xfacta/Automotive-InputOutput-Circuits/Datsun Gauges Complete.kicad_sch

## KiCad design Datsun Gauges Complete.kicad_sch (2024-01-28)

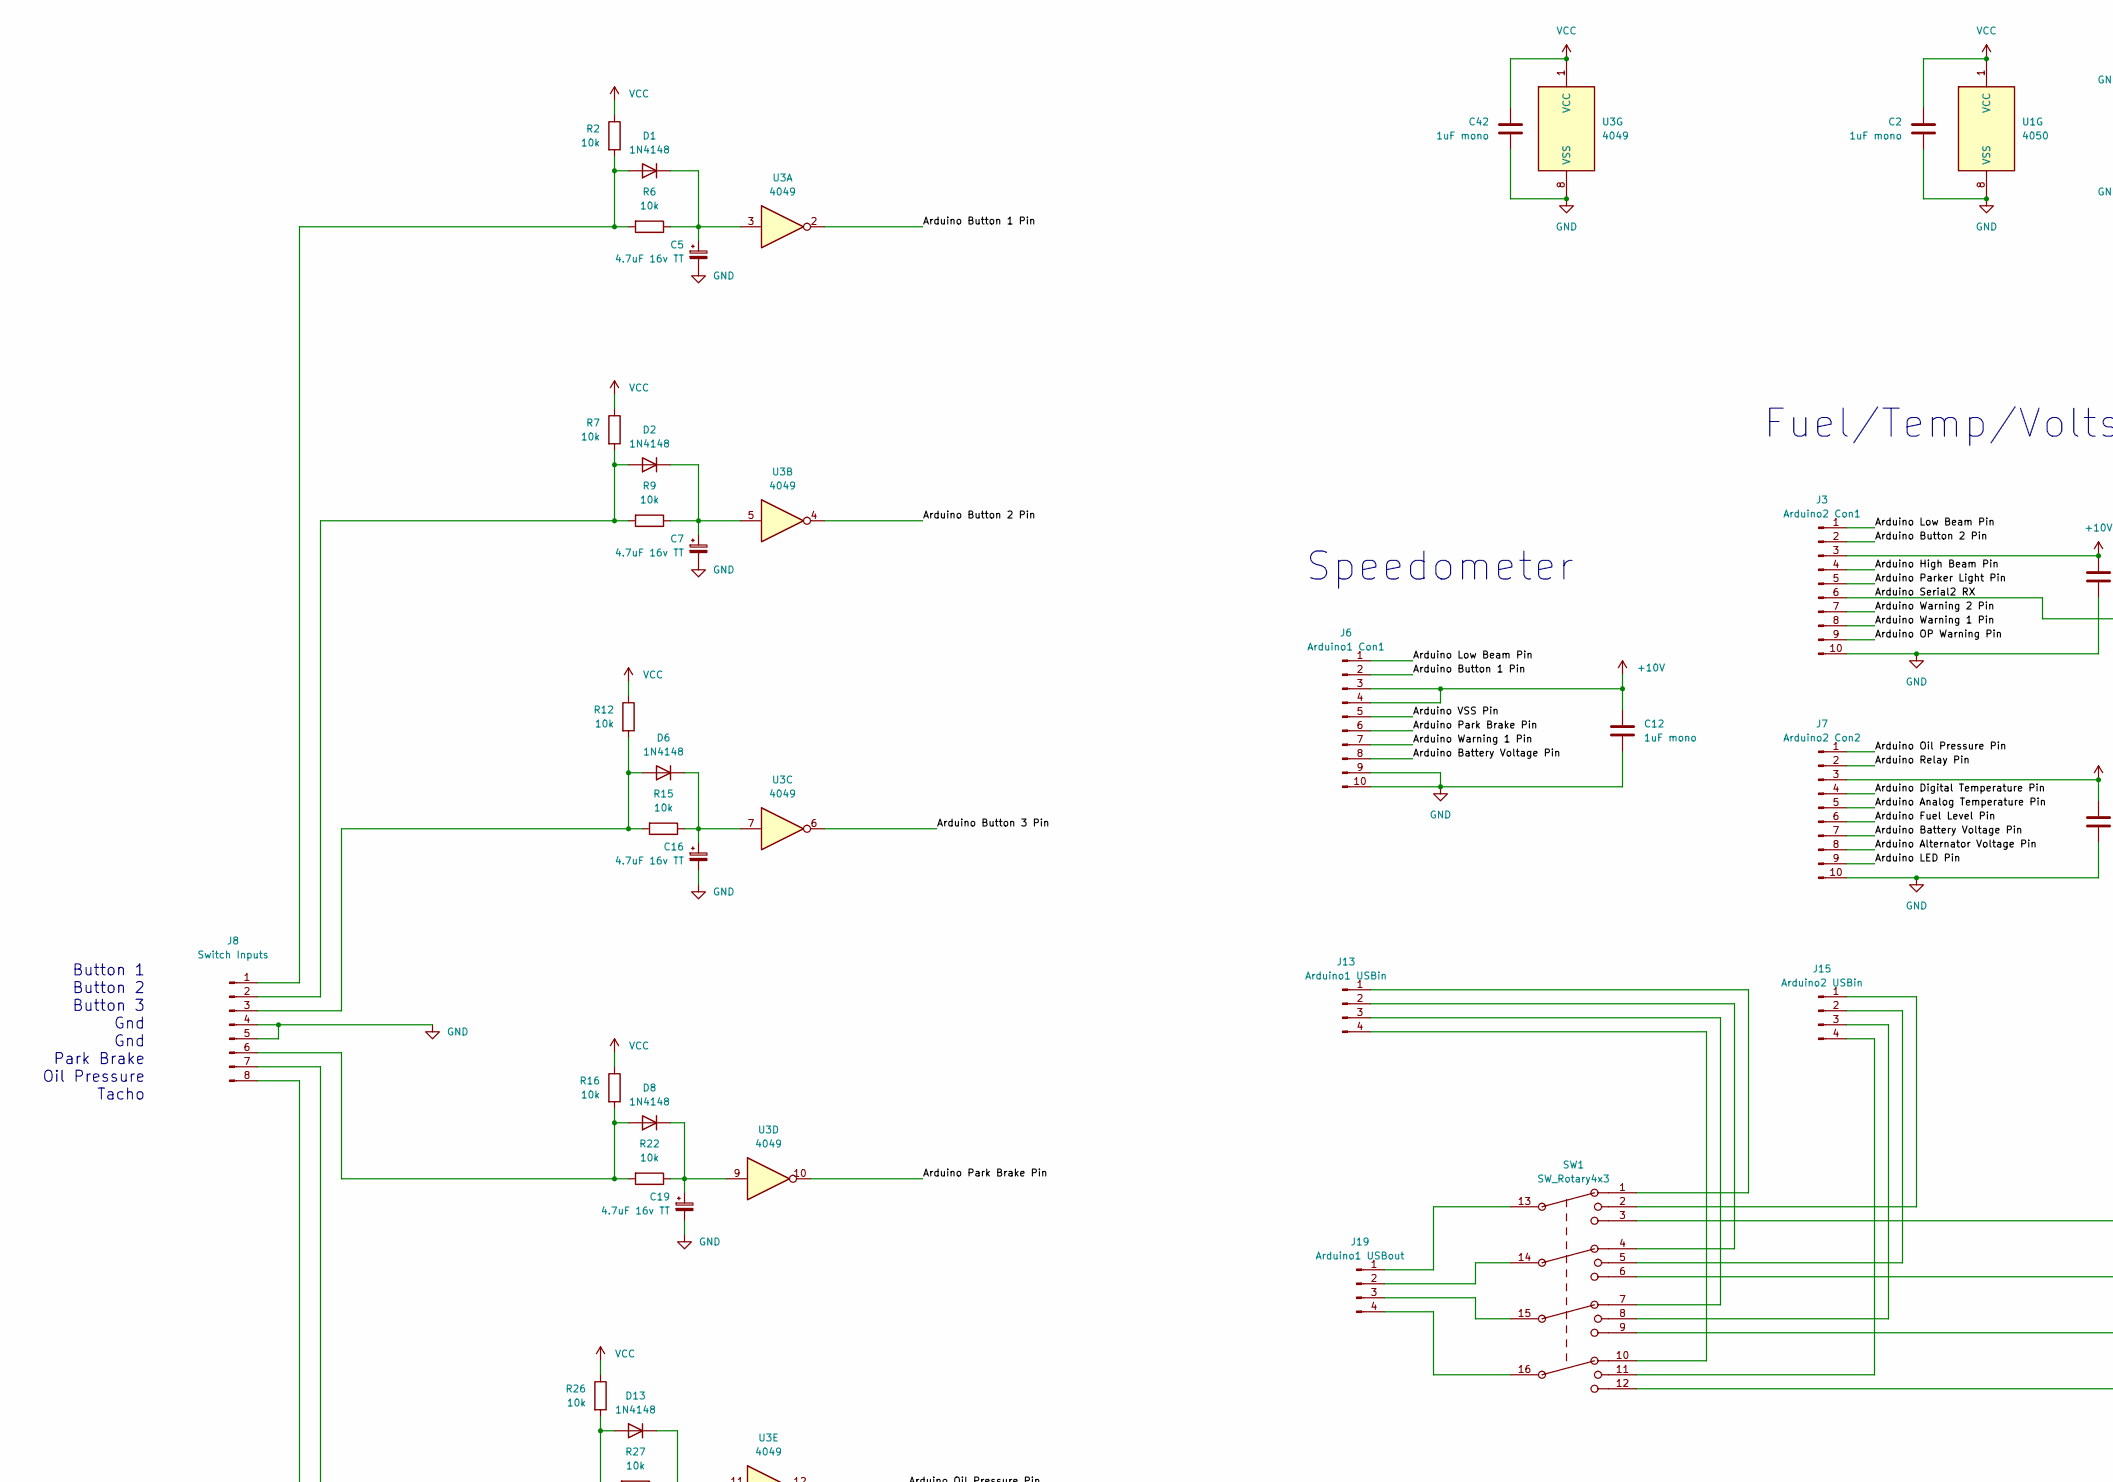
[picture p4: schematic Datsun Gauges Complete.kicad_sch, part in row 1, column 1]

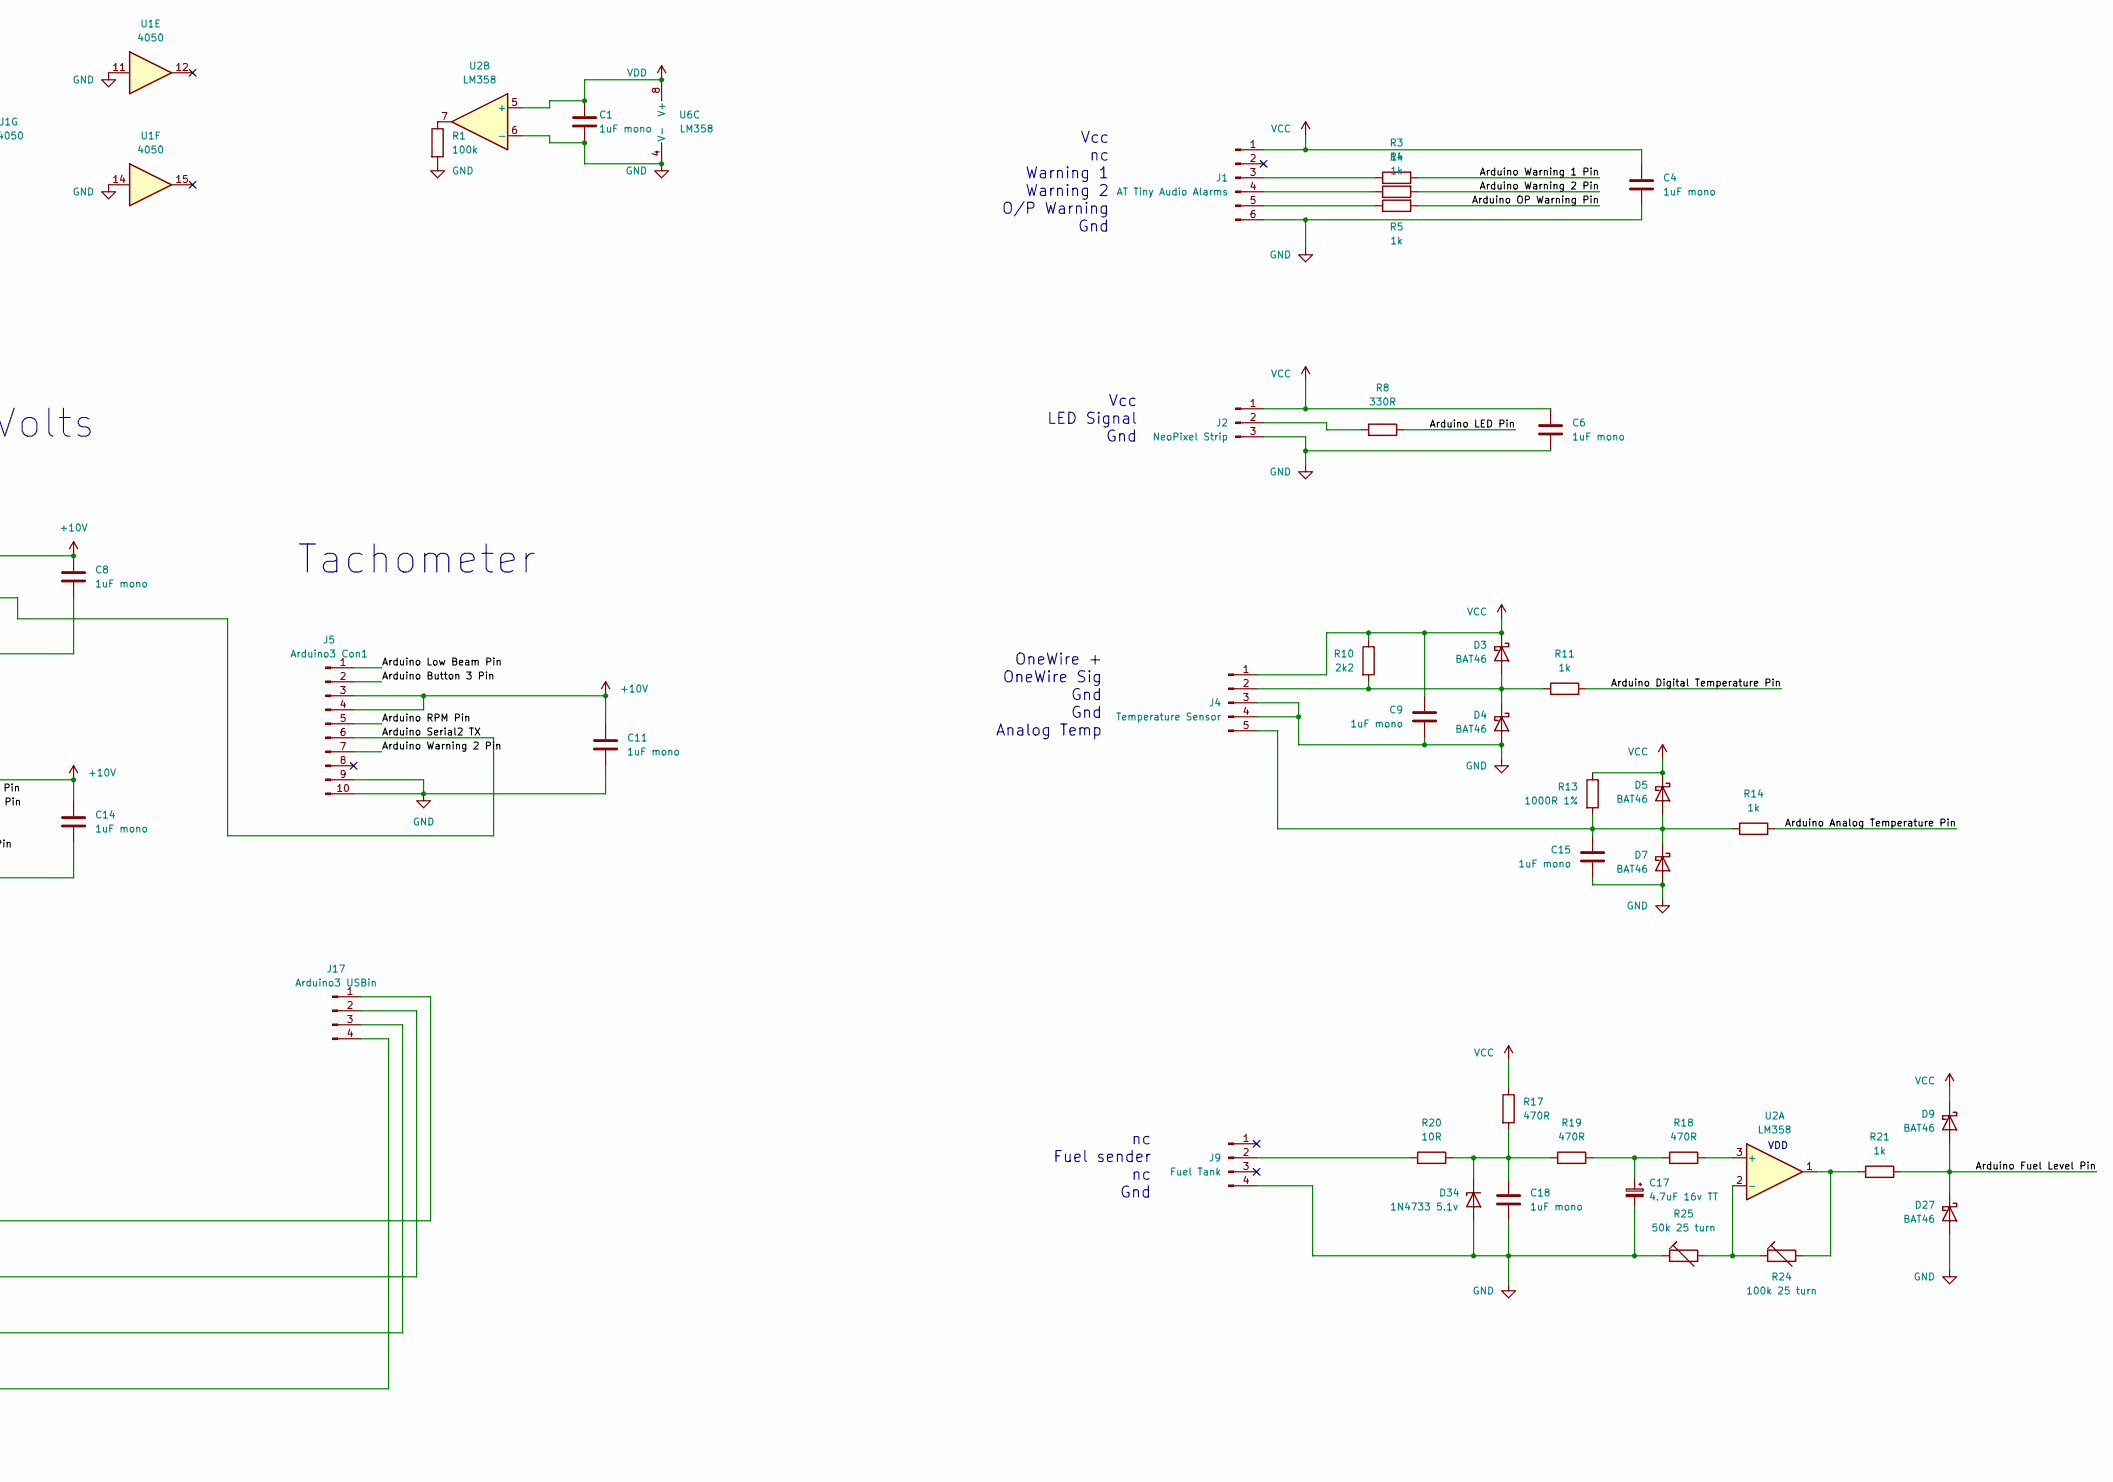
[picture p5: schematic Datsun Gauges Complete.kicad_sch, part in row 1, column 2]

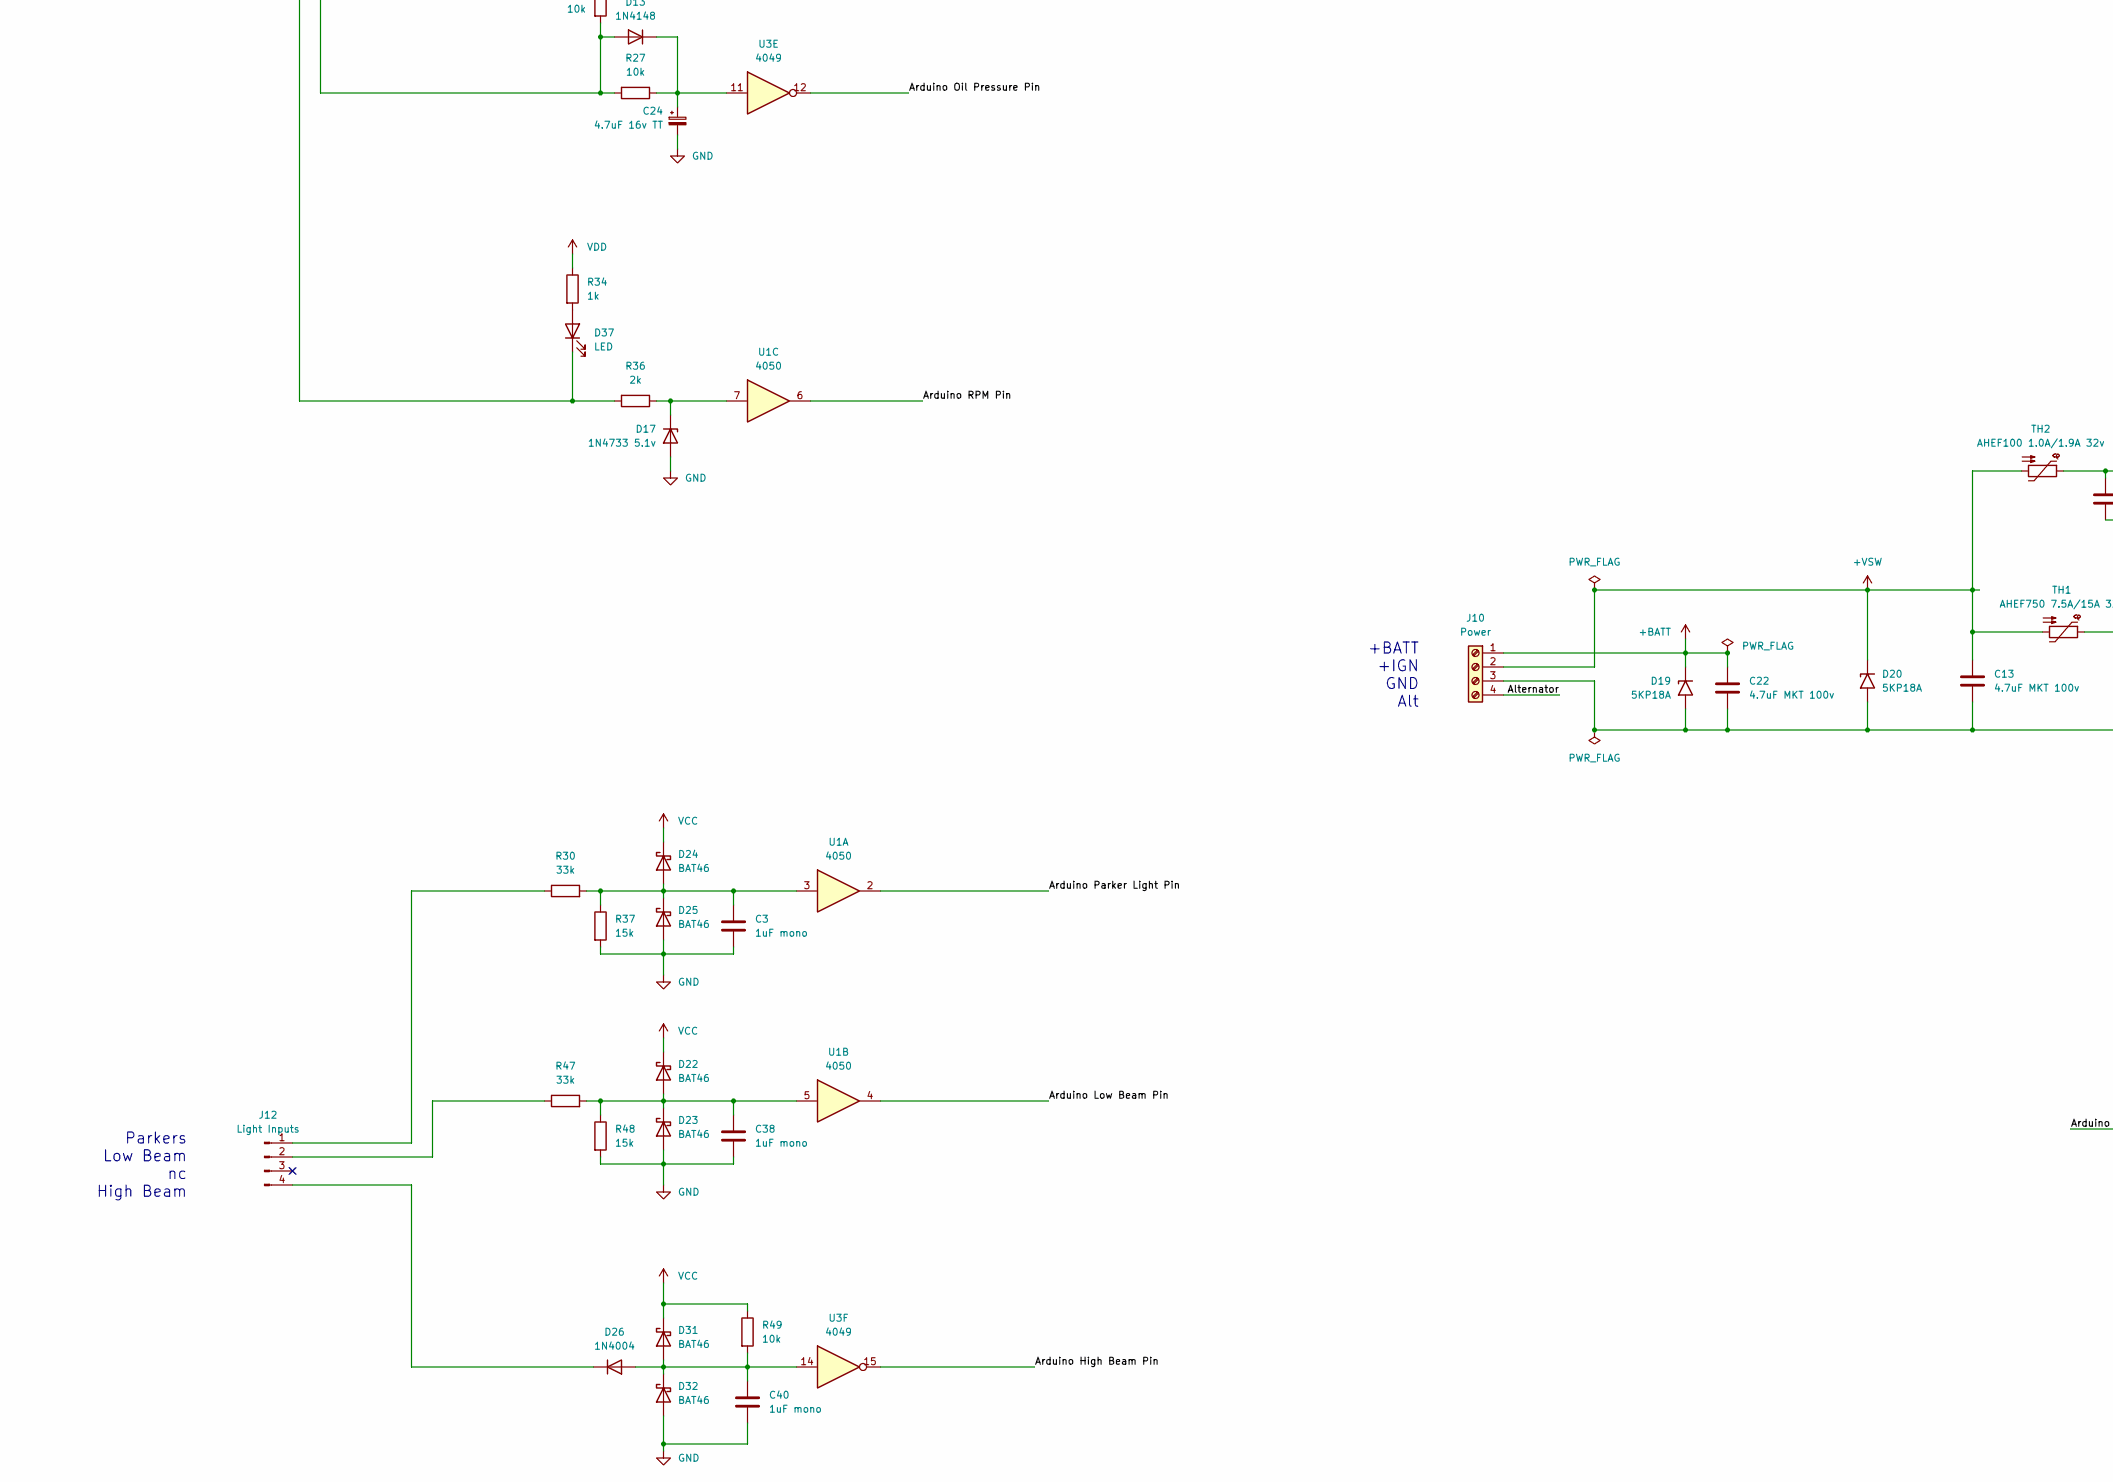
[picture p6: schematic Datsun Gauges Complete.kicad_sch, part in row 2, column 1]

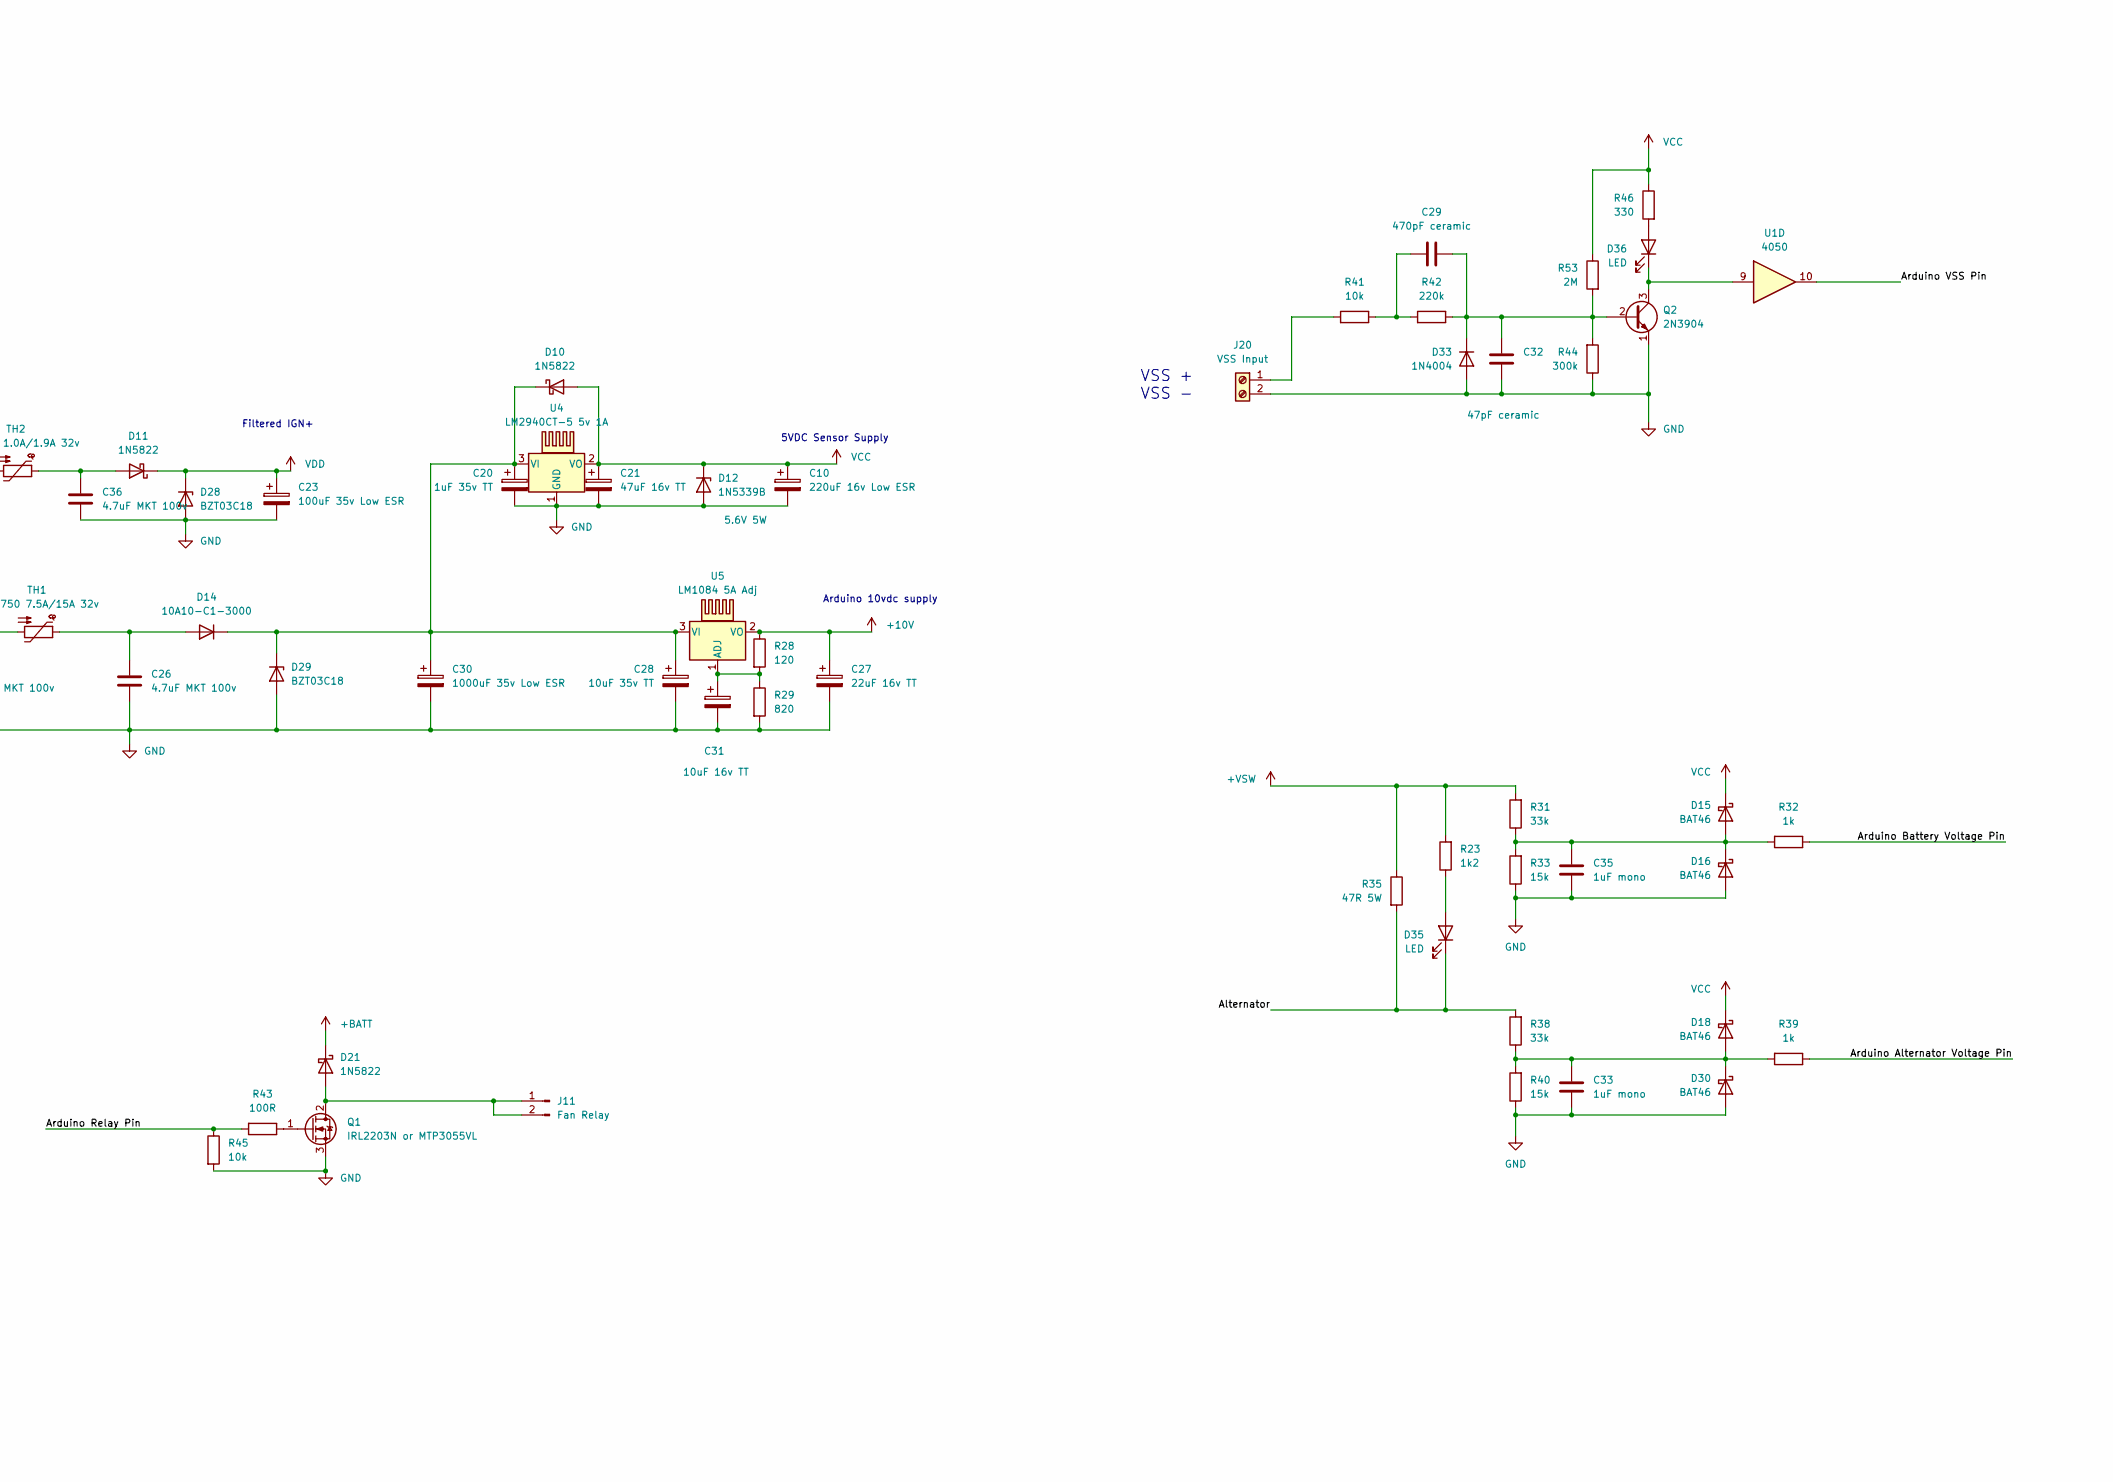
[picture p7: schematic Datsun Gauges Complete.kicad_sch, part in row 2, column 2]

Parts:
C1, C2, C3, C4, C6, C8, C9, C11, C12, C14, C15, C18, C33, C35, C38, C40, C42: 1uF mono; C_Disc_D4.3mm_W1.9mm_P5.00mm
C5, C7, C16, C17, C19, C24: 4.7uF 16v TT; CP_Radial_Tantal_D5.5mm_P5.00mm
C10: 220uF 16v Low ESR; CP_Radial_D8.0mm_P3.50mm
C13, C22, C26, C36: 4.7uF MKT 100v; C_Rect_L26.5mm_W7.0mm_P22.50mm_MKS4
C20: 1uF 35v TT; CP_Radial_Tantal_D5.5mm_P5.00mm
C21: 47uF 16v TT; CP_Radial_Tantal_D5.5mm_P5.00mm
C23: 100uF 35v Low ESR; CP_Radial_D8.0mm_P3.50mm
C27: 22uF 16v TT; CP_Radial_Tantal_D5.5mm_P5.00mm
C28: 10uF 35v TT; CP_Radial_Tantal_D5.5mm_P5.00mm
C29: 470pF ceramic; C_Disc_D4.3mm_W1.9mm_P5.00mm
C30: 1000uF 35v Low ESR; CP_Radial_D16.0mm_P7.50mm
C31: 10uF 16v TT; CP_Radial_Tantal_D5.5mm_P5.00mm
C32: 47pF ceramic; C_Disc_D4.3mm_W1.9mm_P5.00mm
D1, D2, D6, D8, D13: 1N4148; D_DO-35_SOD27_P7.62mm_Horizontal
D3, D4, D5, D7, D9, D15, D16, D18, D22, D23, D24, D25, D27, D30, D31, D32: BAT46; D_DO-41_SOD81_P10.16mm_Horizontal
D10, D11, D21: 1N5822; D_DO-201AD_P15.24mm_Horizontal
D12: 1N5339B; D_DO-201AD_P15.24mm_Horizontal
D14: 10A10-C1-3000; D_P600_R-6_P20.00mm_Horizontal
D17, D34: 1N4733 5.1v; D_DO-41_SOD81_P10.16mm_Horizontal
D19, D20: 5KP18A; D_P600_R-6_P20.00mm_Horizontal
D26, D33: 1N4004; D_DO-41_SOD81_P10.16mm_Horizontal
D28, D29: BZT03C18; D_DO-41_SOD81_P10.16mm_Horizontal
D35, D36, D37: LED
HS1, HS2: Heatsink; Heatsink_Fischer_SK129-STS_42x25mm_2xDrill2.5mm
J1: AT Tiny Audio Alarms; Molex_KK-254_AE-6410-06A_1x06_P2.54mm_Vertical
J2: NeoPixel Strip; Molex_KK-254_AE-6410-03A_1x03_P2.54mm_Vertical
J3: Arduino2 Con1; Molex_KK-254_AE-6410-10A_1x10_P2.54mm_Vertical
J4: Temperature Sensor; Molex_KK-254_AE-6410-05A_1x05_P2.54mm_Vertical
J5: Arduino3 Con1; Molex_KK-254_AE-6410-10A_1x10_P2.54mm_Vertical
J6: Arduino1 Con1; Molex_KK-254_AE-6410-10A_1x10_P2.54mm_Vertical
J7: Arduino2 Con2; Molex_KK-254_AE-6410-10A_1x10_P2.54mm_Vertical
J8: Switch Inputs; Molex_KK-254_AE-6410-10A_1x10_P2.54mm_Vertical
J9: Fuel Tank; Molex_KK-254_AE-6410-04A_1x04_P2.54mm_Vertical
J10: Power; PhoenixContact_GMSTBVA_2,5_4-G-7,62_1x04_P7.62mm_Vertical
J11: Fan Relay; Molex_KK-254_AE-6410-02A_1x02_P2.54mm_Vertical
J12: Light Inputs; Molex_KK-254_AE-6410-02A_1x02_P2.54mm_Vertical
J13: Arduino1 USBin; Molex_KK-254_AE-6410-04A_1x04_P2.54mm_Vertical
J15: Arduino2 USBin; Molex_KK-254_AE-6410-04A_1x04_P2.54mm_Vertical
J17: Arduino3 USBin; Molex_KK-254_AE-6410-04A_1x04_P2.54mm_Vertical
J19: Arduino1 USBout; Molex_KK-254_AE-6410-04A_1x04_P2.54mm_Vertical
J20: VSS Input; PhoenixContact_GMSTBVA_2,5_2-G-7,62_1x02_P7.62mm_Vertical
Q1: IRL2203N or MTP3055VL; TO-220F-3_Vertical
Q2: 2N3904; TO-92_Inline
R1: 100k; R_Axial_DIN0207_L6.3mm_D2.5mm_P10.16mm_Horizontal
R2, R6, R7, R9, R12, R15, R16, R22, R26, R27, R41, R45, R49: 10k; R_Axial_DIN0207_L6.3mm_D2.5mm_P10.16mm_Horizontal
R3, R4, R5, R11, R14, R21, R32, R34, R39: 1k; R_Axial_DIN0207_L6.3mm_D2.5mm_P10.16mm_Horizontal
R8: 330R; R_Axial_DIN0207_L6.3mm_D2.5mm_P10.16mm_Horizontal
R10: 2k2; R_Axial_DIN0207_L6.3mm_D2.5mm_P10.16mm_Horizontal
R13: 1000R 1%; R_Axial_DIN0207_L6.3mm_D2.5mm_P10.16mm_Horizontal
R17, R18, R19: 470R; R_Axial_DIN0207_L6.3mm_D2.5mm_P10.16mm_Horizontal
R20: 10R; R_Axial_DIN0207_L6.3mm_D2.5mm_P10.16mm_Horizontal
R23: 1k2; R_Axial_DIN0207_L6.3mm_D2.5mm_P10.16mm_Horizontal
R24: 100k 25 turn; Potentiometer_Bourns_3296W_Vertical
R25: 50k 25 turn; Potentiometer_Bourns_3296W_Vertical
R28: 120; R_Axial_DIN0207_L6.3mm_D2.5mm_P10.16mm_Horizontal
R29: 820; R_Axial_DIN0207_L6.3mm_D2.5mm_P10.16mm_Horizontal
R30, R31, R38, R47: 33k; R_Axial_DIN0207_L6.3mm_D2.5mm_P10.16mm_Horizontal
R33, R37, R40, R48: 15k; R_Axial_DIN0207_L6.3mm_D2.5mm_P10.16mm_Horizontal
R35: 47R 5W; R_Axial_Power_L20.0mm_W6.4mm_P25.40mm
R36: 2k; R_Axial_DIN0207_L6.3mm_D2.5mm_P10.16mm_Horizontal
R42: 220k; R_Axial_DIN0207_L6.3mm_D2.5mm_P10.16mm_Horizontal
R43: 100R; R_Axial_DIN0207_L6.3mm_D2.5mm_P10.16mm_Horizontal
R44: 300k; R_Axial_DIN0207_L6.3mm_D2.5mm_P10.16mm_Horizontal
R46: 330; R_Axial_DIN0207_L6.3mm_D2.5mm_P10.16mm_Horizontal
R53: 2M; R_Axial_DIN0207_L6.3mm_D2.5mm_P10.16mm_Horizontal
SW1: SW_Rotary4x3
TH1: AHEF750 7.5A/15A 32v; C_Disc_D16.0mm_W5.0mm_P10.00mm
TH2: AHEF100 1.0A/1.9A 32v; C_Disc_D16.0mm_W5.0mm_P10.00mm
U1: 4050; DIP-16_W7.62mm
U2, U6: LM358
U3: 4049; DIP-16_W7.62mm
U4: LM2940CT-5 5v 1A; TO-220-3_Vertical
U5: LM1084 5A Adj; TO-220-3_Vertical

Connections:
+10V: C8.1, C11.1, C12.1, C14.1, C27.1, J3.3, J5.3, J5.4, J6.3, J6.4, J7.3, R28.1, U5.2 (VO)
+BATT: C22.1, D19.1 (A1), D21.1 (K), J10.1
+VSW: C13.1, D20.1 (A1), J10.2, R23.2, R31.2, R35.1, TH1.2, TH2.2
Alternator: D35.1 (K), J10.4, R35.2, R38.2
Arduino Alternator Voltage Pin: J7.8, R39.1
Arduino Analog Temperature Pin: J7.5, R14.2
Arduino Battery Voltage Pin: J6.8, J7.7, R32.1
Arduino Button 1 Pin: J6.2, U3.2
Arduino Button 2 Pin: J3.2, U3.4
Arduino Button 3 Pin: J5.2, U3.6
Arduino Digital Temperature Pin: J7.4, R11.2
Arduino Fuel Level Pin: D9.2 (A), D27.1 (K), J7.6, R21.2
Arduino High Beam Pin: J3.4, U3.15
Arduino LED Pin: J7.9, R8.1
Arduino Low Beam Pin: J3.1, J5.1, J6.1, U1.4
Arduino OP Warning Pin: J3.9, R5.2
Arduino Oil Pressure Pin: J7.1, U3.12
Arduino Park Brake Pin: J6.6, U3.10
Arduino Parker Light Pin: J3.5, U1.2
Arduino RPM Pin: J5.5, U1.6
Arduino Relay Pin: J7.2, R43.2, R45.1
Arduino Serial2 RX: J3.6, J5.6
Arduino VSS Pin: J6.5, U1.10
Arduino Warning 1 Pin: J3.8, J6.7, R3.2
Arduino Warning 2 Pin: J3.7, J5.7, R4.2
GND: C1.2, C2.2, C3.2, C4.2, C5.2, C6.2, C7.2, C8.2, C9.2, C10.2, C11.2, C12.2, C13.2, C14.2, C15.2, C16.2, C17.2, C18.2, C19.2, C20.2, C21.2, C22.2, C23.2, C24.2, C26.2, C27.2, C28.2, C30.2, C31.2, C32.2, C33.2, C35.2, C36.2, C38.2, C40.2, C42.2, D4.2 (A), D7.2 (A), D12.2 (A), D16.2 (A), D17.2 (A), D19.2 (A2), D20.2 (A2), D23.2 (A), D25.2 (A), D27.2 (A), D28.2 (A), D29.2 (A), D30.2 (A), D32.2 (A), D33.2 (A), D34.2 (A), J1.6, J2.3, J3.10, J4.3, J4.4, J5.9, J5.10, J6.9, J6.10, J7.10, J8.4, J8.5, J9.4, J10.3, J20.2, Q1.3 (S), Q2.1 (E), R1.2, R25.1, R29.2, R33.1, R37.2, R40.1, R44.1, R45.2, R48.2, U1.8 (VSS), U1.11, U1.14, U2.6 (-), U3.8 (VSS), U4.1 (GND), U6.4 (V-)
unnamed: C3.1, D24.2 (A), D25.1 (K), R30.2, R37.1, U1.3
unnamed: C5.1, D1.1 (K), R6.1, U3.3
unnamed: C7.1, D2.1 (K), R9.1, U3.5
unnamed: C15.1, D5.2 (A), D7.1 (K), J4.5, R13.2, R14.1
unnamed: C16.1, D6.1 (K), R15.1, U3.7
unnamed: C17.1, R18.1, R19.2
unnamed: C18.1, D34.1 (K), R17.2, R19.1, R20.2
unnamed: C19.1, D8.1 (K), R22.1, U3.9
unnamed: C20.1, C28.1, C30.1, D10.1 (K), D14.1 (K), D29.1 (K), U4.3 (VI), U5.3 (VI)
unnamed: C24.1, D13.1 (K), R27.1, U3.11
unnamed: C26.1, D14.2 (A), TH1.1
unnamed: C29.1, C32.1, D33.1 (K), Q2.2 (B), R42.1, R44.2, R53.2
unnamed: C29.2, R41.1, R42.2
unnamed: C31.1, R28.2, R29.1, U5.1 (ADJ)
unnamed: C33.1, D18.2 (A), D30.1 (K), R38.1, R39.2, R40.2
unnamed: C35.1, D15.2 (A), D16.1 (K), R31.1, R32.2, R33.2
unnamed: C36.1, D11.2 (A), TH2.1
unnamed: C38.1, D22.2 (A), D23.1 (K), R47.2, R48.1, U1.5
unnamed: C40.1, D26.2 (A), D31.2 (A), D32.1 (K), R49.2, U3.14
unnamed: D1.2 (A), J8.1, R2.2, R6.2
unnamed: D2.2 (A), J8.2, R7.2, R9.2
unnamed: D3.2 (A), D4.1 (K), J4.2, R10.2, R11.1
unnamed: D6.2 (A), J8.3, R12.2, R15.2
unnamed: D8.2 (A), J8.6, R16.2, R22.2
unnamed: D13.2 (A), J8.7, R26.2, R27.2
unnamed: D17.1 (K), R36.1, U1.7
unnamed: D21.2 (A), J11.1, J11.2, Q1.2 (D)
unnamed: D26.1 (K), J12.4
unnamed: D35.2 (A), R23.1
unnamed: D36.1 (K), Q2.3 (C), U1.9
unnamed: D36.2 (A), R46.2
unnamed: D37.1 (K), J8.8, R36.2
unnamed: D37.2 (A), R34.2
unnamed: J1.3, R3.1
unnamed: J1.4, R4.1
unnamed: J1.5, R5.1
unnamed: J2.2, R8.2
unnamed: J9.2, R20.1
unnamed: J12.1, R30.1
unnamed: J12.2, R47.1
unnamed: J13.1, SW1.1
unnamed: J13.2, SW1.4
unnamed: J13.3, SW1.7
unnamed: J13.4, SW1.10
unnamed: J15.1, SW1.2
unnamed: J15.2, SW1.5
unnamed: J15.3, SW1.8
unnamed: J15.4, SW1.11
unnamed: J17.1, SW1.3
unnamed: J17.2, SW1.6
unnamed: J17.3, SW1.9
unnamed: J17.4, SW1.12
unnamed: J19.1, SW1.13
unnamed: J19.2, SW1.14
unnamed: J19.3, SW1.15
unnamed: J19.4, SW1.16
unnamed: J20.1, R41.2
unnamed: Q1.1 (G), R43.1
unnamed: R1.1, U2.7
unnamed: R18.2, U2.3 (+)
unnamed: R21.1, R24.2, U2.1
unnamed: R24.1, R25.2, U2.2 (-)
VCC: C2.1, C4.1, C6.1, C9.1, C10.1, C21.1, C42.1, D3.1 (K), D5.1 (K), D9.1 (K), D10.2 (A), D12.1 (K), D15.1 (K), D18.1 (K), D22.1 (K), D24.1 (K), D31.1 (K), J1.1, J2.1, J4.1, R2.1, R7.1, R10.1, R12.1, R13.1, R16.1, R17.1, R26.1, R46.1, R49.1, R53.1, U1.1 (VCC), U3.1 (VCC), U4.2 (VO)
VDD: C1.1, C23.1, D11.1 (K), D28.1 (K), R34.1, U2.5 (+), U6.8 (V+)

Notes on the sheet:
Fuel/Temp/Volts
+BATT +IGN GND Alt
Parkers Low Beam nc High Beam
VDD
VSS + VSS -
Tachometer
5VDC Sensor Supply
OneWire + OneWire Sig Gnd Gnd Analog Temp
Button 1 Button 2 Button 3 Gnd Gnd Park Brake Oil Pressure Tacho
Speedometer
Filtered IGN+
nc Fuel sender nc Gnd
Arduino 10vdc supply
Vcc LED Signal Gnd
Vcc nc Warning 1 Warning 2 O/P Warning Gnd
